ComNets-Bremen/NAVEL/prototypes/Food-Safety-Prototype/design/schematic/schematic.kicad_sch

## KiCad design prototypes/Food-Safety-Prototype/design/schematic/schematic.kicad_sch (2022-05-19)

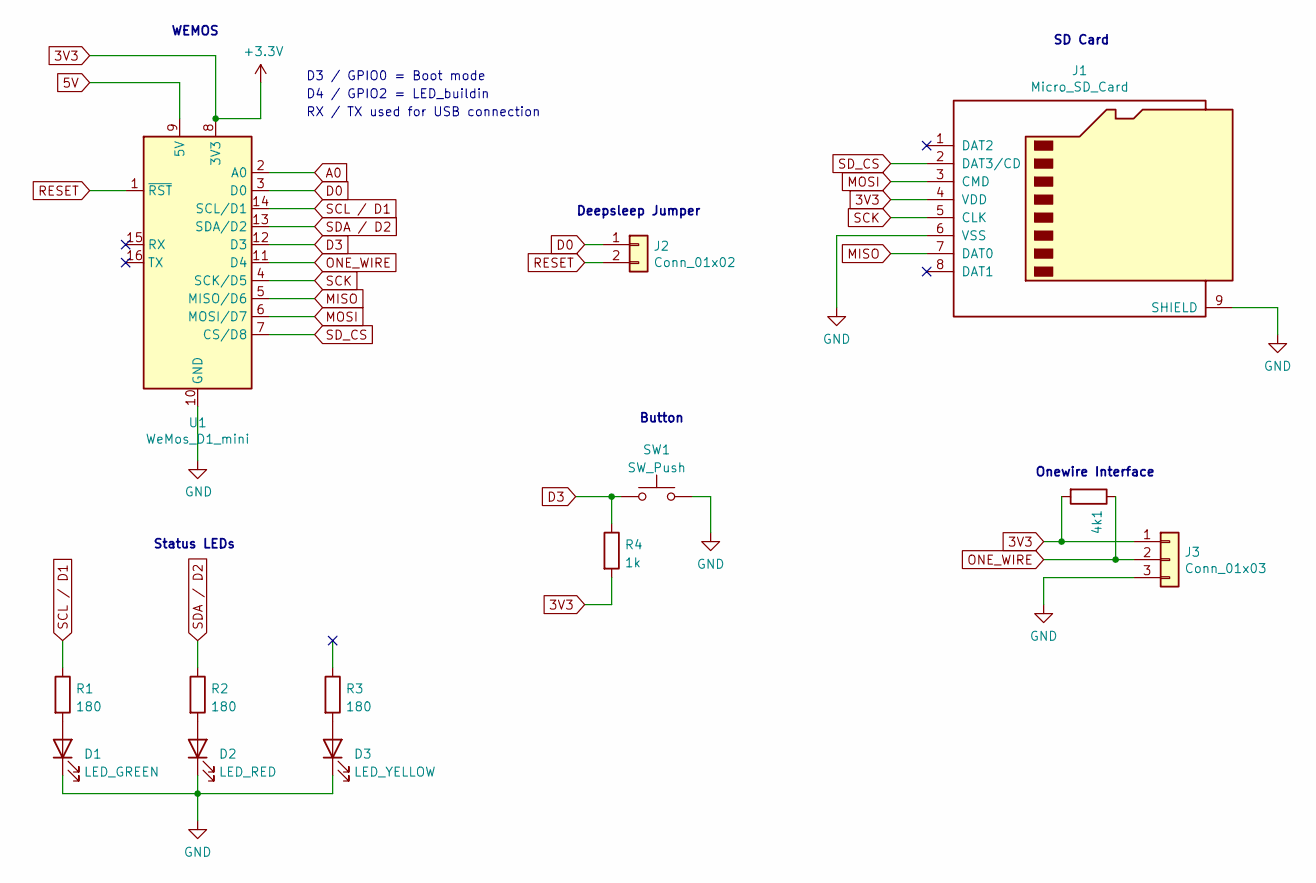
[picture p14: schematic schematic.kicad_sch]

Parts:
4k1: (no value)
D1: LED_GREEN
D2: LED_RED
D3: LED_YELLOW
J1: Micro_SD_Card
J2: Conn_01x02
J3: Conn_01x03
R1, R2, R3: 180
R4: 1k
SW1: SW_Push
U1: WeMos_D1_mini; WEMOS_D1_mini_light

Connections:
5V: U1.9 (5V)
+3.3V: 4k1.2, J1.4 (VDD), J3.1, R4.2, U1.8 (3V3)
A0: U1.2 (A0)
D0: J2.1, U1.3 (D0)
D3: R4.1, SW1.1, U1.12 (D3)
GND: D1.1 (K), D2.1 (K), D3.1 (K), J1.6 (VSS), J1.9 (SHIELD), J3.3, SW1.2, U1.10 (GND)
MISO: J1.7 (DAT0), U1.5 (MISO/D6)
MOSI: J1.3 (CMD), U1.6 (MOSI/D7)
unnamed: D1.2 (A), R1.2
unnamed: D2.2 (A), R2.2
unnamed: D3.2 (A), R3.2
ONE_WIRE: 4k1.1, J3.2, U1.11 (D4)
RESET: J2.2, U1.1 (~RST)
SCK: J1.5 (CLK), U1.4 (SCK/D5)
SCL / D1: R1.1, U1.14 (SCL/D1)
SDA / D2: R2.1, U1.13 (SDA/D2)
SD_CS: J1.2 (DAT3/CD), U1.7 (CS/D8)

Notes on the sheet:
WEMOS
Button
RX / TX used for USB connection
Onewire Interface
D3 / GPIO0 = Boot mode
Status LEDs
SD Card
Deepsleep Jumper
D4 / GPIO2 = LED_buildin
